fourks/cps2_digiav/rtl/syncgen.v

//
// Copyright (C) 2016-2018  Markus Hiienkari <mhiienka@niksula.hut.fi>
//
// This file is part of CPS2 Digital AV Interface project.
//
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

`include "cps3_defines.v"

`define NUM_LINE_BUFFERS        40

module syncgen (
    input PCLK,
    input reset_n,
    input HSYNC_ref,
    input VSYNC_ref,
    input [31:0] h_info,
    input [31:0] v_info,
    input aspect,
    output reg HSYNC_out,
    output reg VSYNC_out,
    output reg DE_out,
    output reg [11:0] hcnt, //max. 4096
    output reg [10:0] vcnt, //max. 2048
    output reg [8:0] hcnt_lbuf,
    output reg [5:0] vcnt_lbuf,
    output reg mask_enable,
    output reg [2:0] h_ctr,
    output reg [2:0] v_ctr
);

parameter   H_SYNCLEN       =   44;
parameter   H_BACKPORCH     =   148;
parameter   H_ACTIVE        =   1920;
parameter   H_TOTAL         =   2200;
parameter   V_SYNCLEN       =   5;
parameter   V_BACKPORCH     =   36;
parameter   V_ACTIVE        =   1080;
parameter   V_TOTAL         =   1125;

parameter   X_START     =   H_SYNCLEN + H_BACKPORCH;
parameter   Y_START     =   V_SYNCLEN + V_BACKPORCH;

parameter h_mult_std = 4;
parameter h_mult_wide = 4;
parameter v_ctr_max = 4;

reg [3:0] V_OFFSET;
reg [10:0] V_INITLINE;

reg prev_hs, prev_vs;
reg v_leadedge, v_leadedge_synced;

reg [7:0] V_gen;
reg frameid;

reg [8:0] h_active_src;
reg [10:0] h_width_dst;
reg [2:0] h_mult;
reg [8:0] h_padding;

wire [8:0] hcnt_lbuf_resetpos = (aspect == `CPS3_ASP_STD) ? 0 : 8;

// HSYNC gen (negative polarity)
always @(posedge PCLK or negedge reset_n)
begin
    if (!reset_n) begin
        hcnt <= 0;
        hcnt_lbuf <= 0;
        HSYNC_out <= 0;
        prev_hs <= 1'b1;
        prev_vs <= 1'b1;
        v_leadedge <= 0;
        v_leadedge_synced <= 0;
    end else begin
        // Hsync counter
        if (!v_leadedge_synced && (prev_vs == 1'b1) && (VSYNC_ref == 1'b0)) begin
            v_leadedge <= 1;
        end else if ((v_leadedge == 1'b1) && (prev_hs == 1'b1) && (HSYNC_ref == 1'b0)) begin
            v_leadedge <= 0;
            v_leadedge_synced <= 1;
            hcnt <= 0;
            h_ctr <= 0;
            hcnt_lbuf <= hcnt_lbuf_resetpos;
        end else if (hcnt < H_TOTAL-1) begin
            hcnt <= hcnt + 1;
            if (hcnt >= X_START + H_ACTIVE - h_padding) begin
                mask_enable <= 1'b1;
            end else if (hcnt >= X_START + h_padding) begin
                h_ctr <= (h_ctr == h_mult-1) ? 0 : (h_ctr + 1'b1);
                hcnt_lbuf <= (h_ctr == h_mult-1) ? (hcnt_lbuf + 1'b1) : hcnt_lbuf;
                mask_enable <= 1'b0;
            end
        end else begin
            hcnt <= 0;
            h_ctr <= 0;
            hcnt_lbuf <= hcnt_lbuf_resetpos;
        end
        
        // Hsync signal
        HSYNC_out <= (hcnt < H_SYNCLEN) ? 0 : 1;
        
        prev_hs <= HSYNC_ref;
        prev_vs <= VSYNC_ref;
    end
end

// VSYNC gen (negative polarity)
always @(posedge PCLK or negedge reset_n)
begin
    if (!reset_n) begin
        vcnt <= 0;
        VSYNC_out <= 0;
    end else begin
        if (v_leadedge == 1'b1) begin
            vcnt <= V_INITLINE;
        end else if (hcnt == H_TOTAL-1) begin
            // Vsync counter
            if (vcnt < V_TOTAL-1 )
                vcnt <= vcnt + 1;
            else
                vcnt <= 0;
            
            if (vcnt == Y_START-1) begin
                vcnt_lbuf <= V_OFFSET;
                v_ctr <= 0;
            end else if (v_ctr == v_ctr_max) begin
                if (vcnt_lbuf < `NUM_LINE_BUFFERS-1)
                    vcnt_lbuf <= (vcnt_lbuf + 1'b1);
                else
                    vcnt_lbuf <= 0;
                    
                v_ctr <= 0;
            end else begin
                v_ctr <= v_ctr + 1'b1;
            end

            // Vsync signal
            VSYNC_out <= (vcnt < V_SYNCLEN) ? 0 : 1;
        end
    end
end

// Read config
always @(posedge PCLK) begin
    if (VSYNC_ref == 1'b0) begin
        V_OFFSET <= v_info[3:0];
        V_INITLINE <= v_info[14:4];
        h_mult <= (aspect == `CPS3_ASP_WIDE) ? h_mult_wide : h_mult_std;
        h_active_src <= (aspect == `CPS3_ASP_WIDE) ? `CPS3_H_ACTIVE_WIDE : `CPS3_H_ACTIVE_STD;
        h_width_dst <= h_mult*h_active_src;
        h_padding <= (h_width_dst <= H_ACTIVE) ? ((H_ACTIVE-h_width_dst)/2) : 0;
    end
end

// DE gen
always @(posedge PCLK or negedge reset_n)
begin
    if (!reset_n)
        DE_out <= 1'b0;
    else
        DE_out <= (hcnt >= X_START && hcnt < X_START + H_ACTIVE && vcnt >= Y_START && vcnt < Y_START + V_ACTIVE);
end

endmodule
