fourks/cps2_digiav/rtl/fir_2ch_audio_sim/fir_2ch_audio_param.txt

PhysChanIn : 1 
PhysChanOut : 1 
ChansPerPhyIn : 2 
ChansPerPhyOut : 2 
InWidth : 17 
InFracWidth : 0 
OutWidth : 24 
OutFullWidth : 31 
OutFracWidth : 0 
OutFullFracWidth : 0 
nChans : 16 
nTaps : 16 
clockRate : 24.576 
inRate : 1.536 
interpN : 1 
decimN : 16 
busDataWidth : 16 
bankInWidth : 0 
modeWidth : 0 
